telzo2000/cool536azcore/img/img00011.jpg

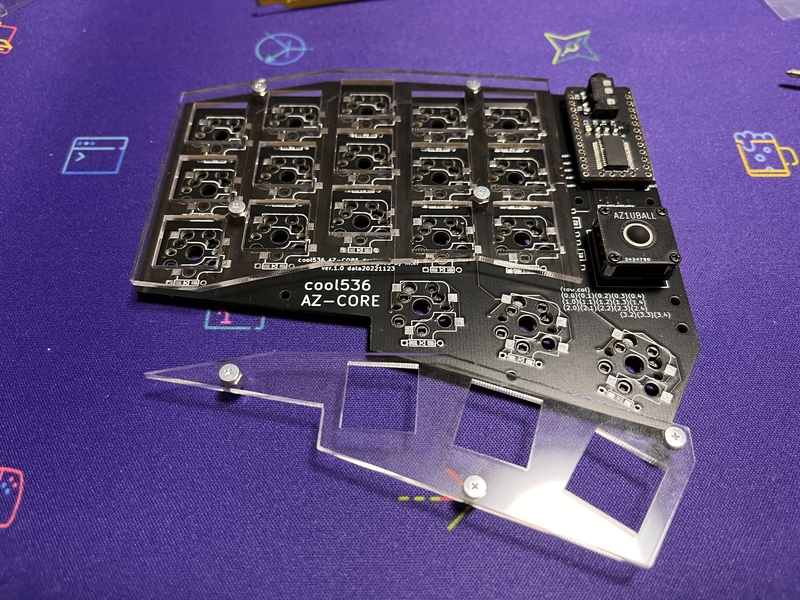
img/img00011.jpg
