telzo2000/cool536azcore/img/img00029.jpg

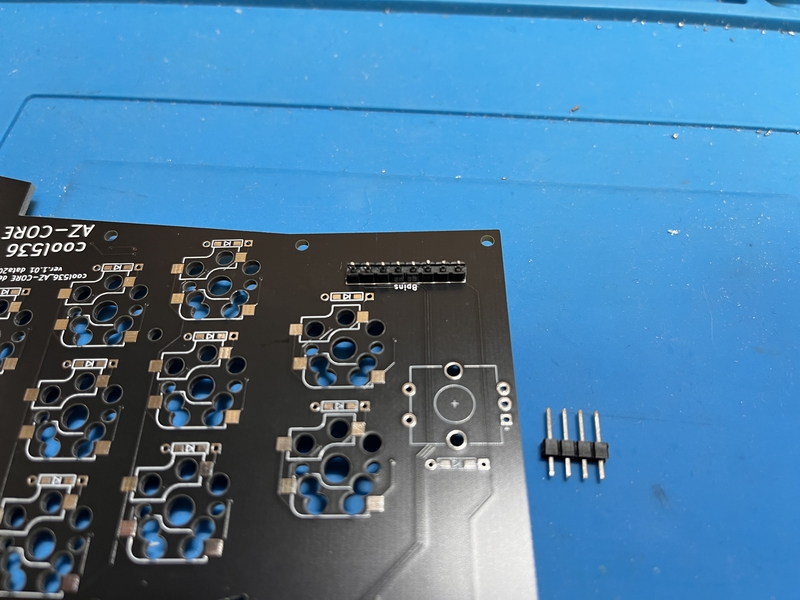
img/img00029.jpg
